xusixteen/EleksTube_IPS/Firmeware/src/common.cpp

#include "common.h"
#include "network.h"

boolean doDelayMillisTime(unsigned long interval, unsigned long *previousMillis, boolean state)
{
    unsigned long currentMillis = millis();
    if (currentMillis - *previousMillis >= interval)
    {
        *previousMillis = currentMillis;
        state = !state;
    }
    return state;
}
